slash128v6/DC32_Cnet_Badge/Docs/Photos/Screenshot 2024-05-24 153021.png

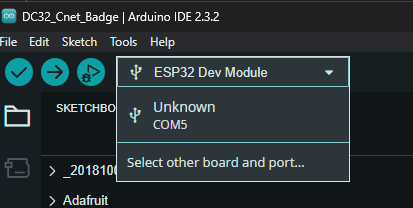
Docs/Photos/Screenshot 2024-05-24 153021.png
