slash128v6/DC32_Cnet_Badge/Software/ESP32-WROOM-32-Development-Board-5V-TYPE-C-CH340C-WiFi-Bluetooth-Ultra-Low-Power-Consumption-SPI.webp

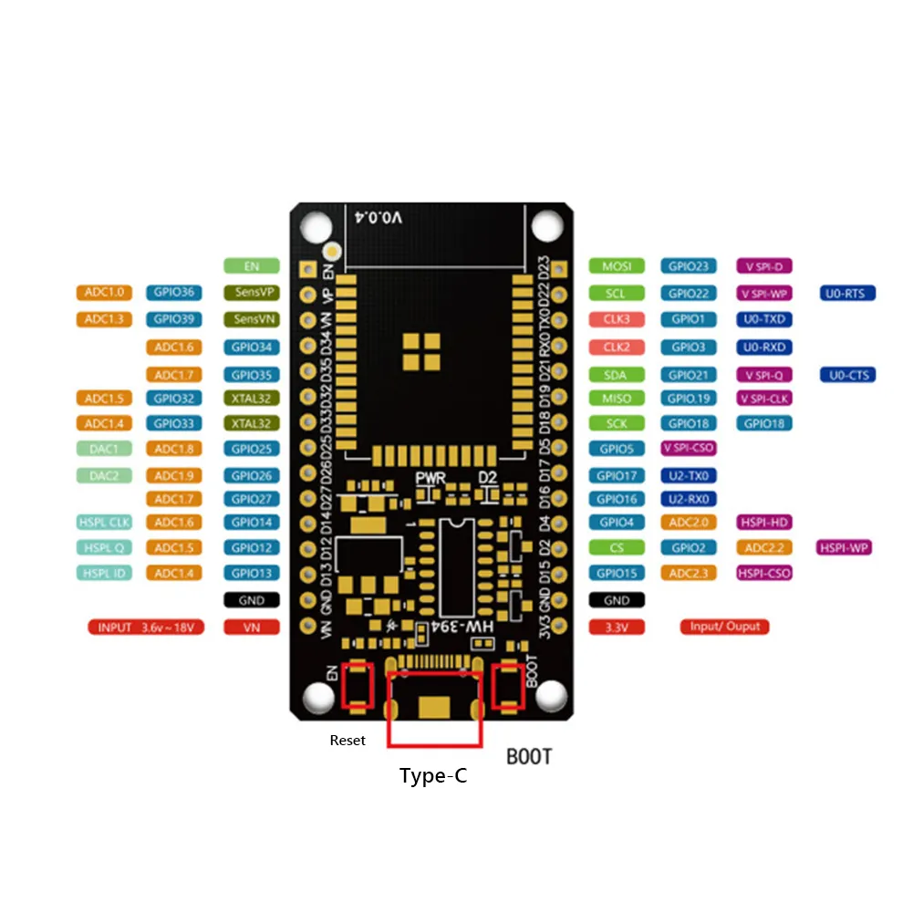
Software/ESP32-WROOM-32-Development-Board-5V-TYPE-C-CH340C-WiFi-Bluetooth-Ultra-Low-Power-Consumption-SPI.webp
